electrobs/mil_time_clock/docs/manual/sources/button.pdf

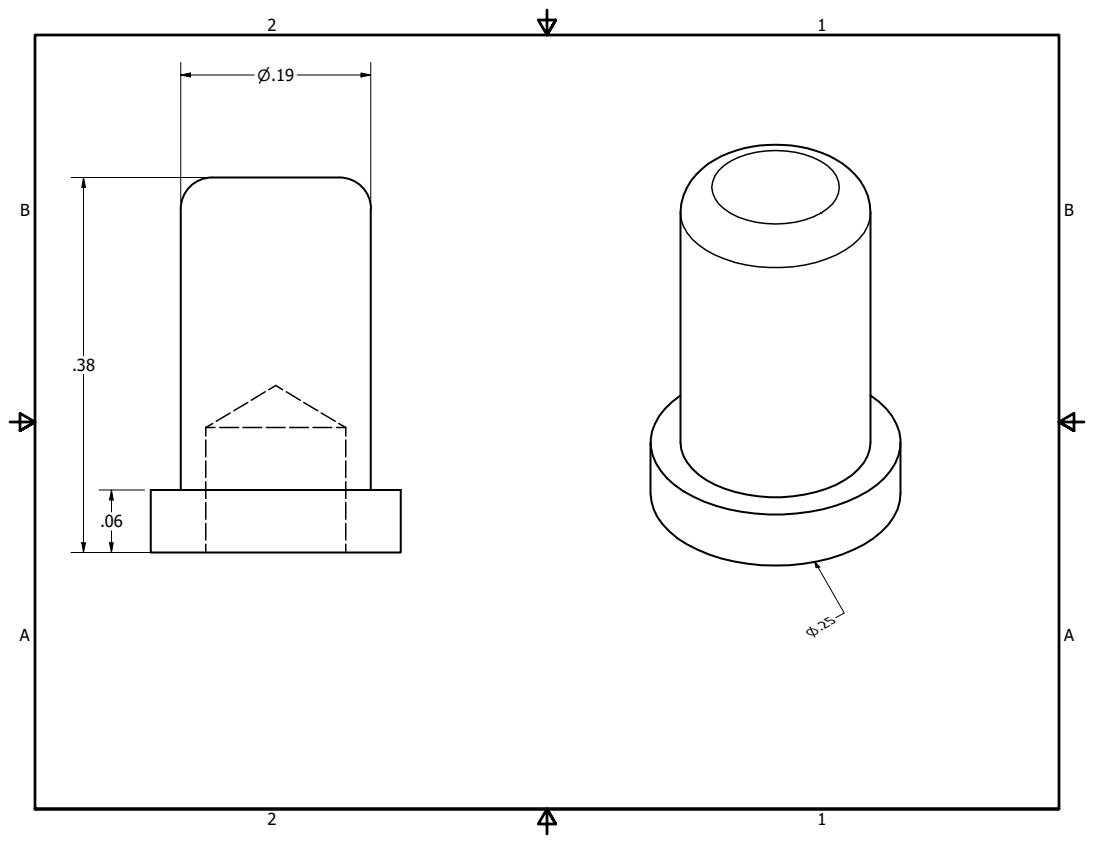
[picture p31: page 1]
