electrobs/mil_time_clock/docs/manual/sources/Case_Front.pdf

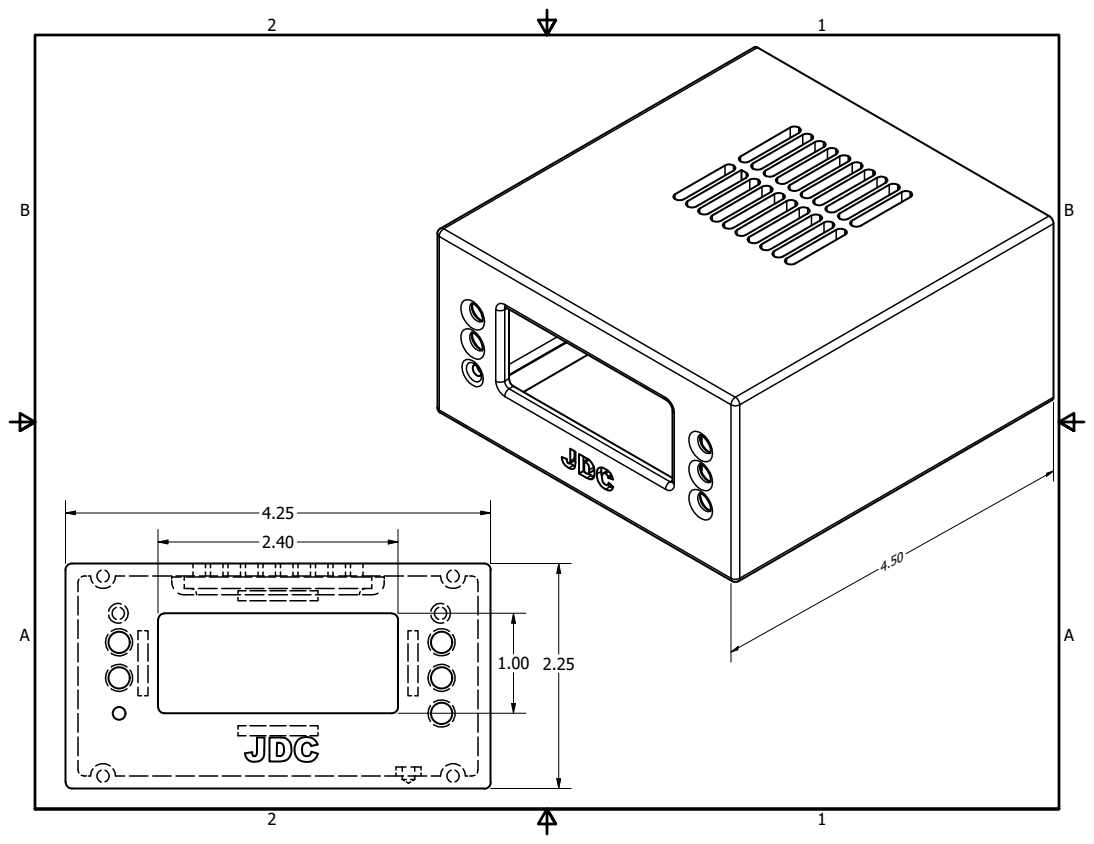
[picture p32: page 1]
