electrobs/mil_time_clock/docs/manual/sources/Case_Rear.pdf

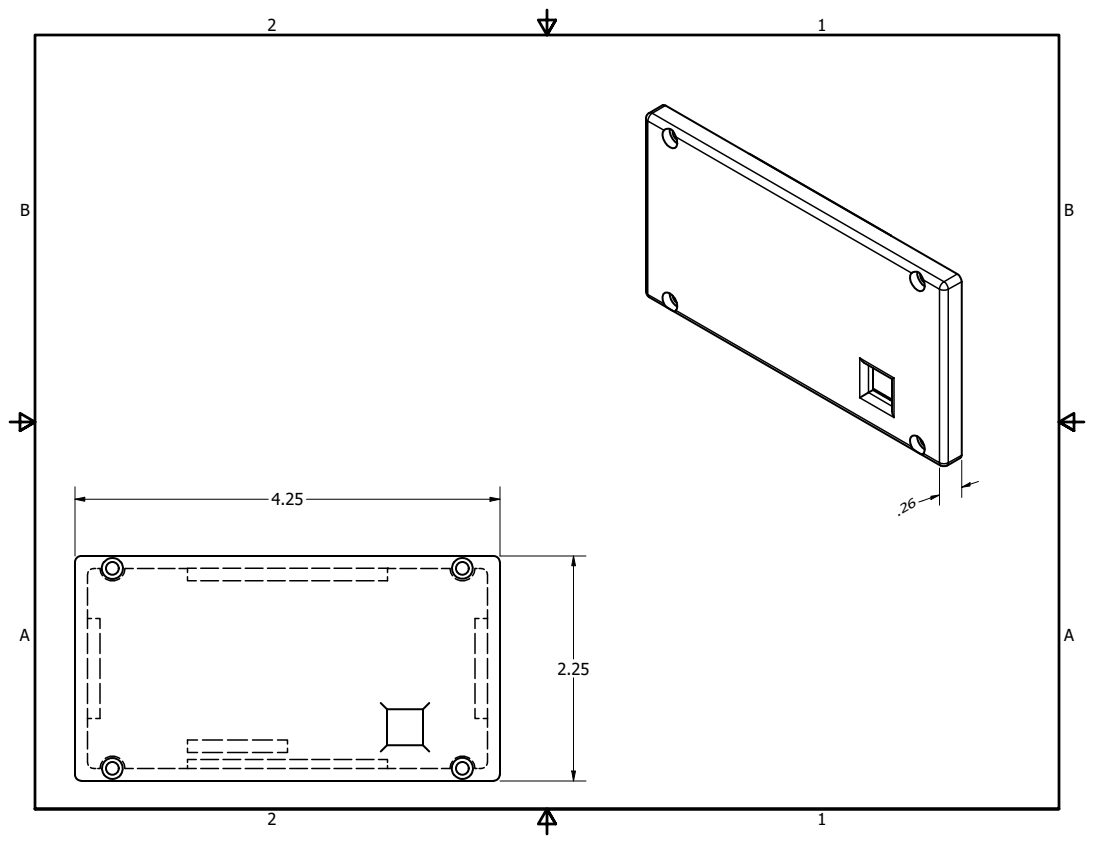
[picture p33: page 1]
